cscashby/esp32-showcontrol/src/esp32-showcontrol/src/config_json.h

const char CONFIG_JSON[] PROGMEM = R"=====(
{
  "network": {
    "hostname": "esp32-showcontrol",
    "master_host": {
      "name": "ca-mbp",
      "host": "10.18.100.102",
      "port": 53000
    },
    "secondary_hosts": [
      {
        "name": "secondary-dummy",
        "host": "192.168.5.104",
        "port": 53000
      }
    ],
    "osc_listen_port": 53001
  },
  "general": {
    "timers" : {
      "led_flash_ms": 1000,
      "switch_debounce_ms": 200,
      "heartbeat_timeout_ms": 1500,
      "heartbeat_us": 200000,
      "poll_us": 100000
    },
    "start_osc" : [
      {
        "string": "/updates",
        "arg_int": 1
      },
      {
        "string": "/alwaysReply",
        "arg_int": 1
      },
      {
        "string": "/runningOrPausedCues"
      },
      {
        "string": "/cue/selected/displayName"
      }
    ]
  },
  "buttons": {
    "go": {
      "LED_pin": 0,
      "Button_pin": 33,
      "OSC_messages": [
        "/stop",
        "/go",
        "/runningOrPausedCues"
      ]
    },
    "stop": {
      "LED_pin": 15,
      "Button_pin": 35,
      "OSC_messages": [
        "/stop"
      ]
    },
    "pause": {
      "LED_pin": 13,
      "LED_inverted": true,
      "Button_pin": 34,
      "OSC_messages": [
        "/pause",
        "/playhead/previous"
      ]
    },
    "previous": {
      "LED_pin": 16,
      "Button_pin": 36,
      "OSC_messages": [
        "/stop",
        "/playhead/previous"
      ]
    },
    "next": {
      "LED_pin": 32,
      "Button_pin": 39,
      "OSC_messages": [
        "/playhead/next"
      ]
    }
  }
}
)=====";
